kptristan24/OneClockToRuleThemAll/reqDoc/GanttChart/gantt_chart_11_9_16.pdf

ID | Task Name | Task Lead | Start | Finish | Duration | Q4 16 | Q1 17 | Q2 17
11/6 | 11/13 | 11/20 | 11/27 | 12/4 | 12/11 | 12/18 | 12/25 | 1/1 | 1/8 | 1/15 | 1/22 | 1/29 | 2/5 | 2/12 | 2/19 | 2/26 | 3/5 | 3/12 | 3/19 | 3/26 | 4/2 | 4/9 | 4/16 | 4/23
1 | RTC Research | Scott | 11/7/2016 | 12/16/2016 | 30d
Materials Research | 11/7/2016 | 1/5/2017 | 44d
2 | LED Research | 11/7/2016 | 12/16/2016 | 30d
3 | Microcontroller Research | 11/7/2016 | 12/16/2016 | 30d
External Power | 2/15/2017 | 3/1/2017 | 11d

5

6

8

Scott

Taz

Tristan

Taz

9

Fabrication | Scott | 3/15/2017 | 4/28/2017 | 33d
Hardware Intercommunication | Whole Team | 12/23/2016 | 1/11/2017 | 14d
Grid Layout | Tristan | 2/16/2017 | 3/15/2017 | 20d

4

Basic Display Control Software | Taz | 1/11/2017 | 1/30/2017 | 14d
Advanced Display Modes | Scott | 1/30/2017 | 3/10/2017 | 30d
7 | Timing Logic | Tristan | 1/11/2017 | 2/21/2017 | 30d
Human Interface Software | Taz | 1/30/2017 | 3/31/2017 | 45d

11

12

13

10 | Additional Software Features | Whole Team | 1/30/2017 | 4/21/2017 | 60d
14 | Software Testing | Tristan | 3/15/2017 | 4/28/2017 | 33d
